pschauppner/ElevenFingers/pictures/PXL_20220617_202617205.jpg

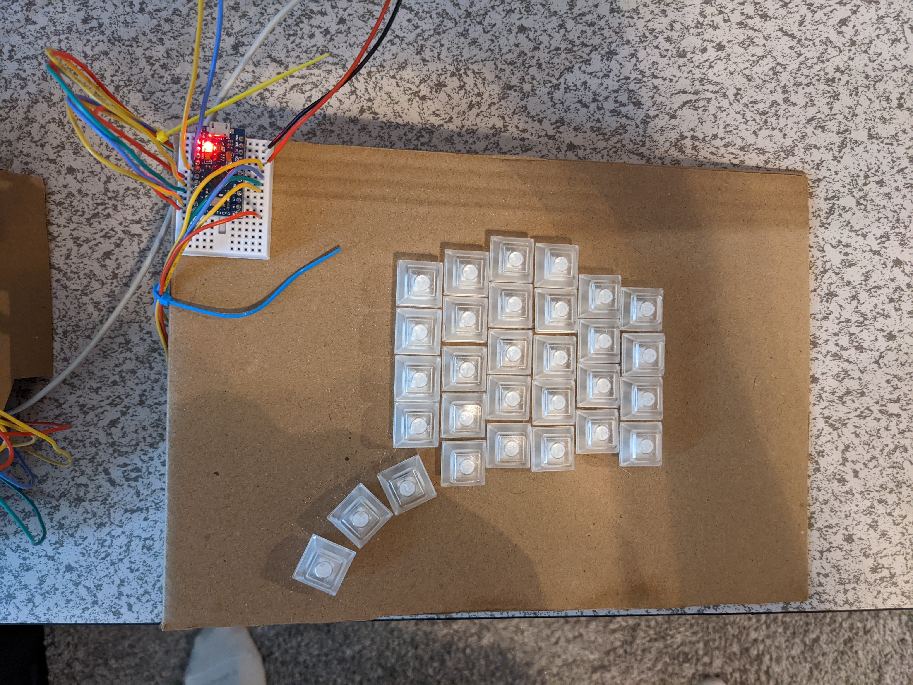
pictures/PXL_20220617_202617205.jpg
